ChrisJP-Embedded/midiSequencerInputUnit/Hardware/MidiSequencerInputUnit_6R_8C/Controller_Switch_Matrix_Module.kicad_sch

## KiCad design Hardware/MidiSequencerInputUnit_6R_8C/Controller_Switch_Matrix_Module.kicad_sch (2023-01-30)

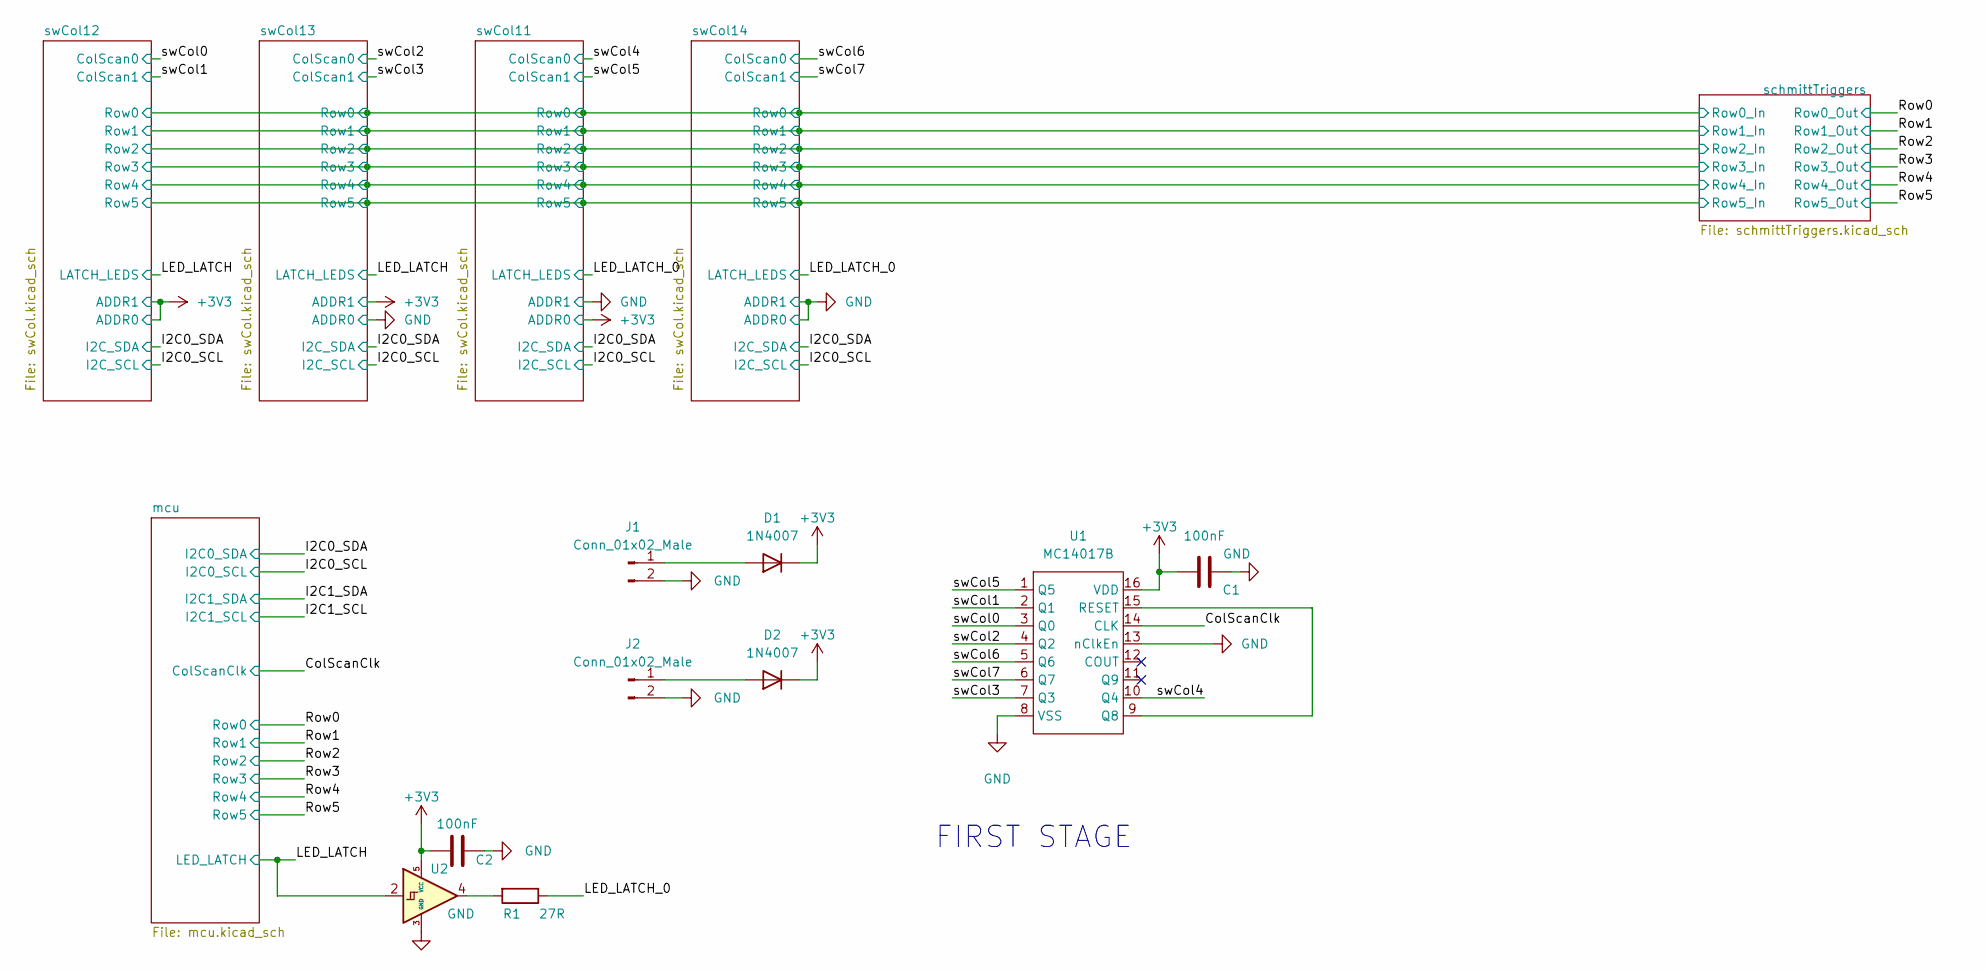
[picture p2: schematic Controller_Switch_Matrix_Module.kicad_sch]

Parts:
C1, C2: 100nF; C_0603_1608Metric; LCSC C14663
D1, D2: 1N4007; D_DO-41_SOD81_P10.16mm_Horizontal
J1, J2: Conn_01x02_Male; PinHeader_1x02_P2.54mm_Horizontal
R1: 27R; R_0603_1608Metric; LCSC C25190
U1: MC14017B; SOIC-16_3.9x9.9mm_P1.27mm; LCSC C512979
U2: SN74LVC1G17; SOT-23-5_HandSoldering; LCSC C7836

Connections:
+3V3: C1.1, C2.1, D1.1 (K), D2.1 (K), U1.16 (VDD), U2.5 (VCC)
ColScanClk: U1.14 (CLK)
GND: C1.2, C2.2, J1.2, J2.2, U1.8 (VSS), U1.13 (nClkEn), U2.3 (GND)
LED_LATCH: U2.2
LED_LATCH_0: R1.1
unnamed: D1.2 (A), J1.1
unnamed: D2.2 (A), J2.1
unnamed: R1.2, U2.4
unnamed: U1.9 (Q8), U1.15 (RESET)
swCol0: U1.3 (Q0)
swCol1: U1.2 (Q1)
swCol2: U1.4 (Q2)
swCol3: U1.7 (Q3)
swCol4: U1.10 (Q4)
swCol5: U1.1 (Q5)
swCol6: U1.5 (Q6)
swCol7: U1.6 (Q7)

Notes on the sheet:
FIRST STAGE
