ChrisJP-Embedded/midiSequencerInputUnit/Hardware/MidiSequencerInputUnit_6R_8C/Encoders.kicad_sch

## KiCad design Hardware/MidiSequencerInputUnit_6R_8C/Encoders.kicad_sch (2023-01-30)

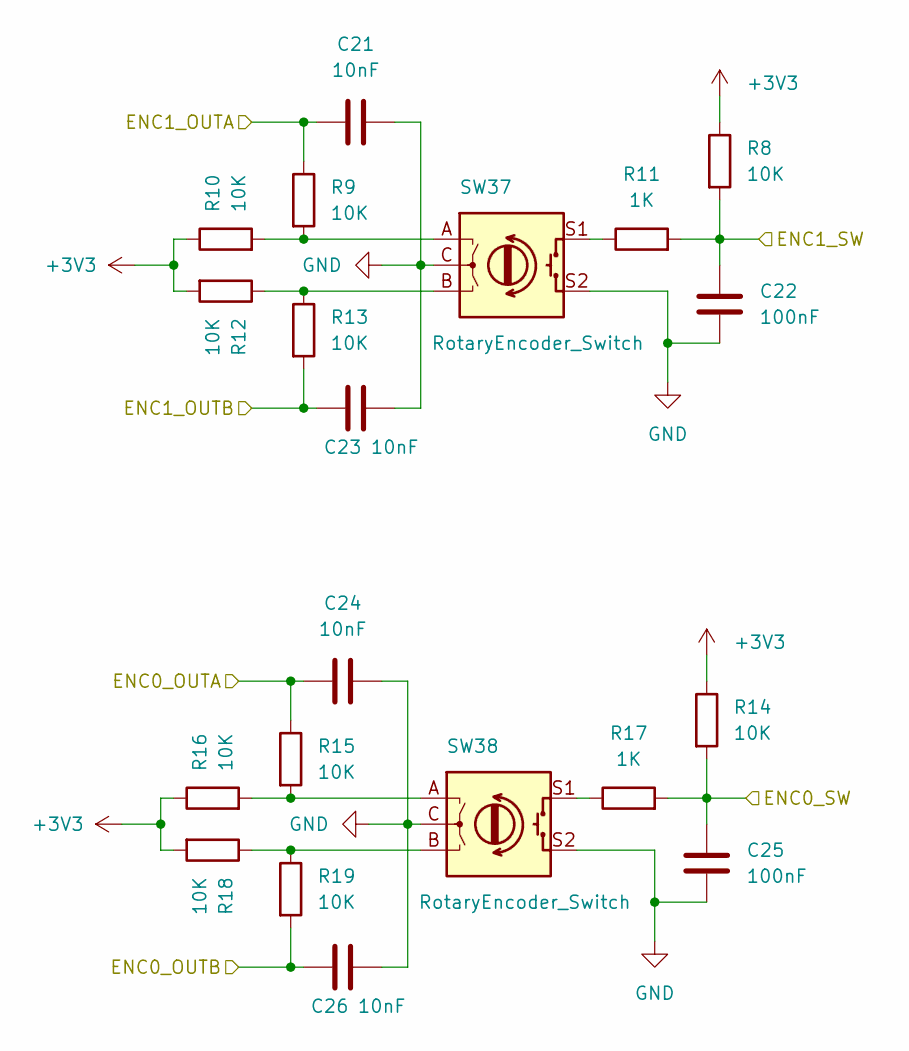
[picture p3: schematic Encoders.kicad_sch]

Parts:
C21, C23, C24, C26: 10nF; C_0603_1608Metric; LCSC C57112
C22, C25: 100nF; C_0603_1608Metric; LCSC C14663
R8, R9, R10, R12, R13, R14, R15, R16, R18, R19: 10K; R_0603_1608Metric; LCSC C25804
R11, R17: 1K; R_0603_1608Metric; LCSC C21190
SW37, SW38: RotaryEncoder_Switch; PEC11R-4220K-S0024

Connections:
+3V3: R8.1, R10.1, R12.2, R14.1, R16.1, R18.2
ENC0_OUTA: C24.1, R15.1
ENC0_OUTB: C26.1, R19.2
ENC0_SW: C25.1, R14.2, R17.2
ENC1_OUTA: C21.1, R9.1
ENC1_OUTB: C23.1, R13.2
ENC1_SW: C22.1, R8.2, R11.2
GND: C21.2, C22.2, C23.2, C24.2, C25.2, C26.2, SW37.C, SW37.S2, SW38.C, SW38.S2
unnamed: R9.2, R10.2, SW37.A
unnamed: R11.1, SW37.S1
unnamed: R12.1, R13.1, SW37.B
unnamed: R15.2, R16.2, SW38.A
unnamed: R17.1, SW38.S1
unnamed: R18.1, R19.1, SW38.B
