ChrisJP-Embedded/midiSequencerInputUnit/Hardware/MidiSequencerInputUnit_6R_8C/ips_screen.kicad_sch

## KiCad design Hardware/MidiSequencerInputUnit_6R_8C/ips_screen.kicad_sch (2023-01-30)

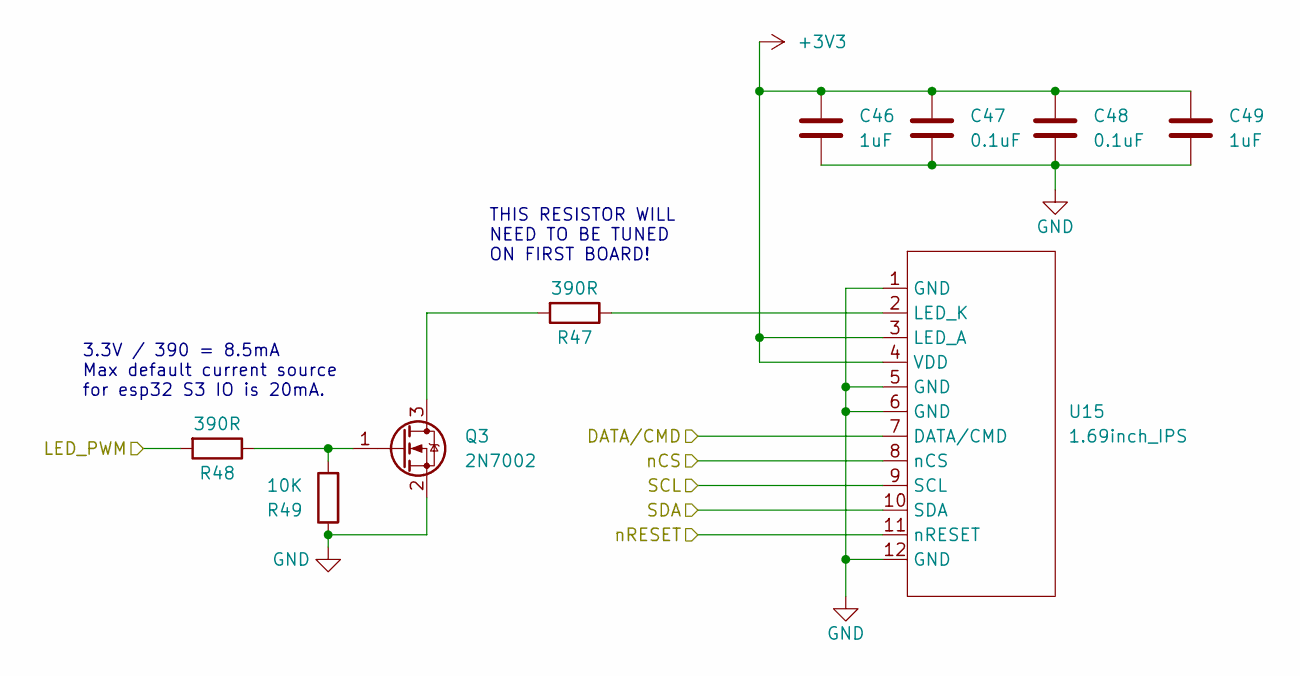
[picture p4: schematic ips_screen.kicad_sch]

Parts:
C46, C49: 1uF; C_0603_1608Metric; LCSC C15849
C47, C48: 0.1uF; C_0603_1608Metric; LCSC C14663
Q3: 2N7002; SOT-23; LCSC C8545
R47, R48: 390R; R_0603_1608Metric; LCSC C23151
R49: 10K; R_0603_1608Metric; LCSC C25804
U15: 1.69inch_IPS; 1.69inch IPS

Connections:
+3V3: C46.1, C47.1, C48.1, C49.1, U15.3 (LED_A), U15.4 (VDD)
DATA/CMD: U15.7 (DATA/CMD)
GND: C46.2, C47.2, C48.2, C49.2, Q3.2 (S), R49.1, U15.1 (GND), U15.5 (GND), U15.6 (GND), U15.12 (GND)
LED_PWM: R48.2
unnamed: Q3.1 (G), R48.1, R49.2
unnamed: Q3.3 (D), R47.2
unnamed: R47.1, U15.2 (LED_K)
SCL: U15.9 (SCL)
SDA: U15.10 (SDA)
nCS: U15.8 (nCS)
nRESET: U15.11 (nRESET)

Notes on the sheet:
3.3V / 390 = 8.5mA Max default current source for esp32 S3 IO is 20mA.
THIS RESISTOR WILL NEED TO BE TUNED ON FIRST BOARD!
