ChrisJP-Embedded/midiSequencerInputUnit/Hardware/MidiSequencerInputUnit_6R_8C/mcu.kicad_sch

## KiCad design Hardware/MidiSequencerInputUnit_6R_8C/mcu.kicad_sch (2023-01-30)

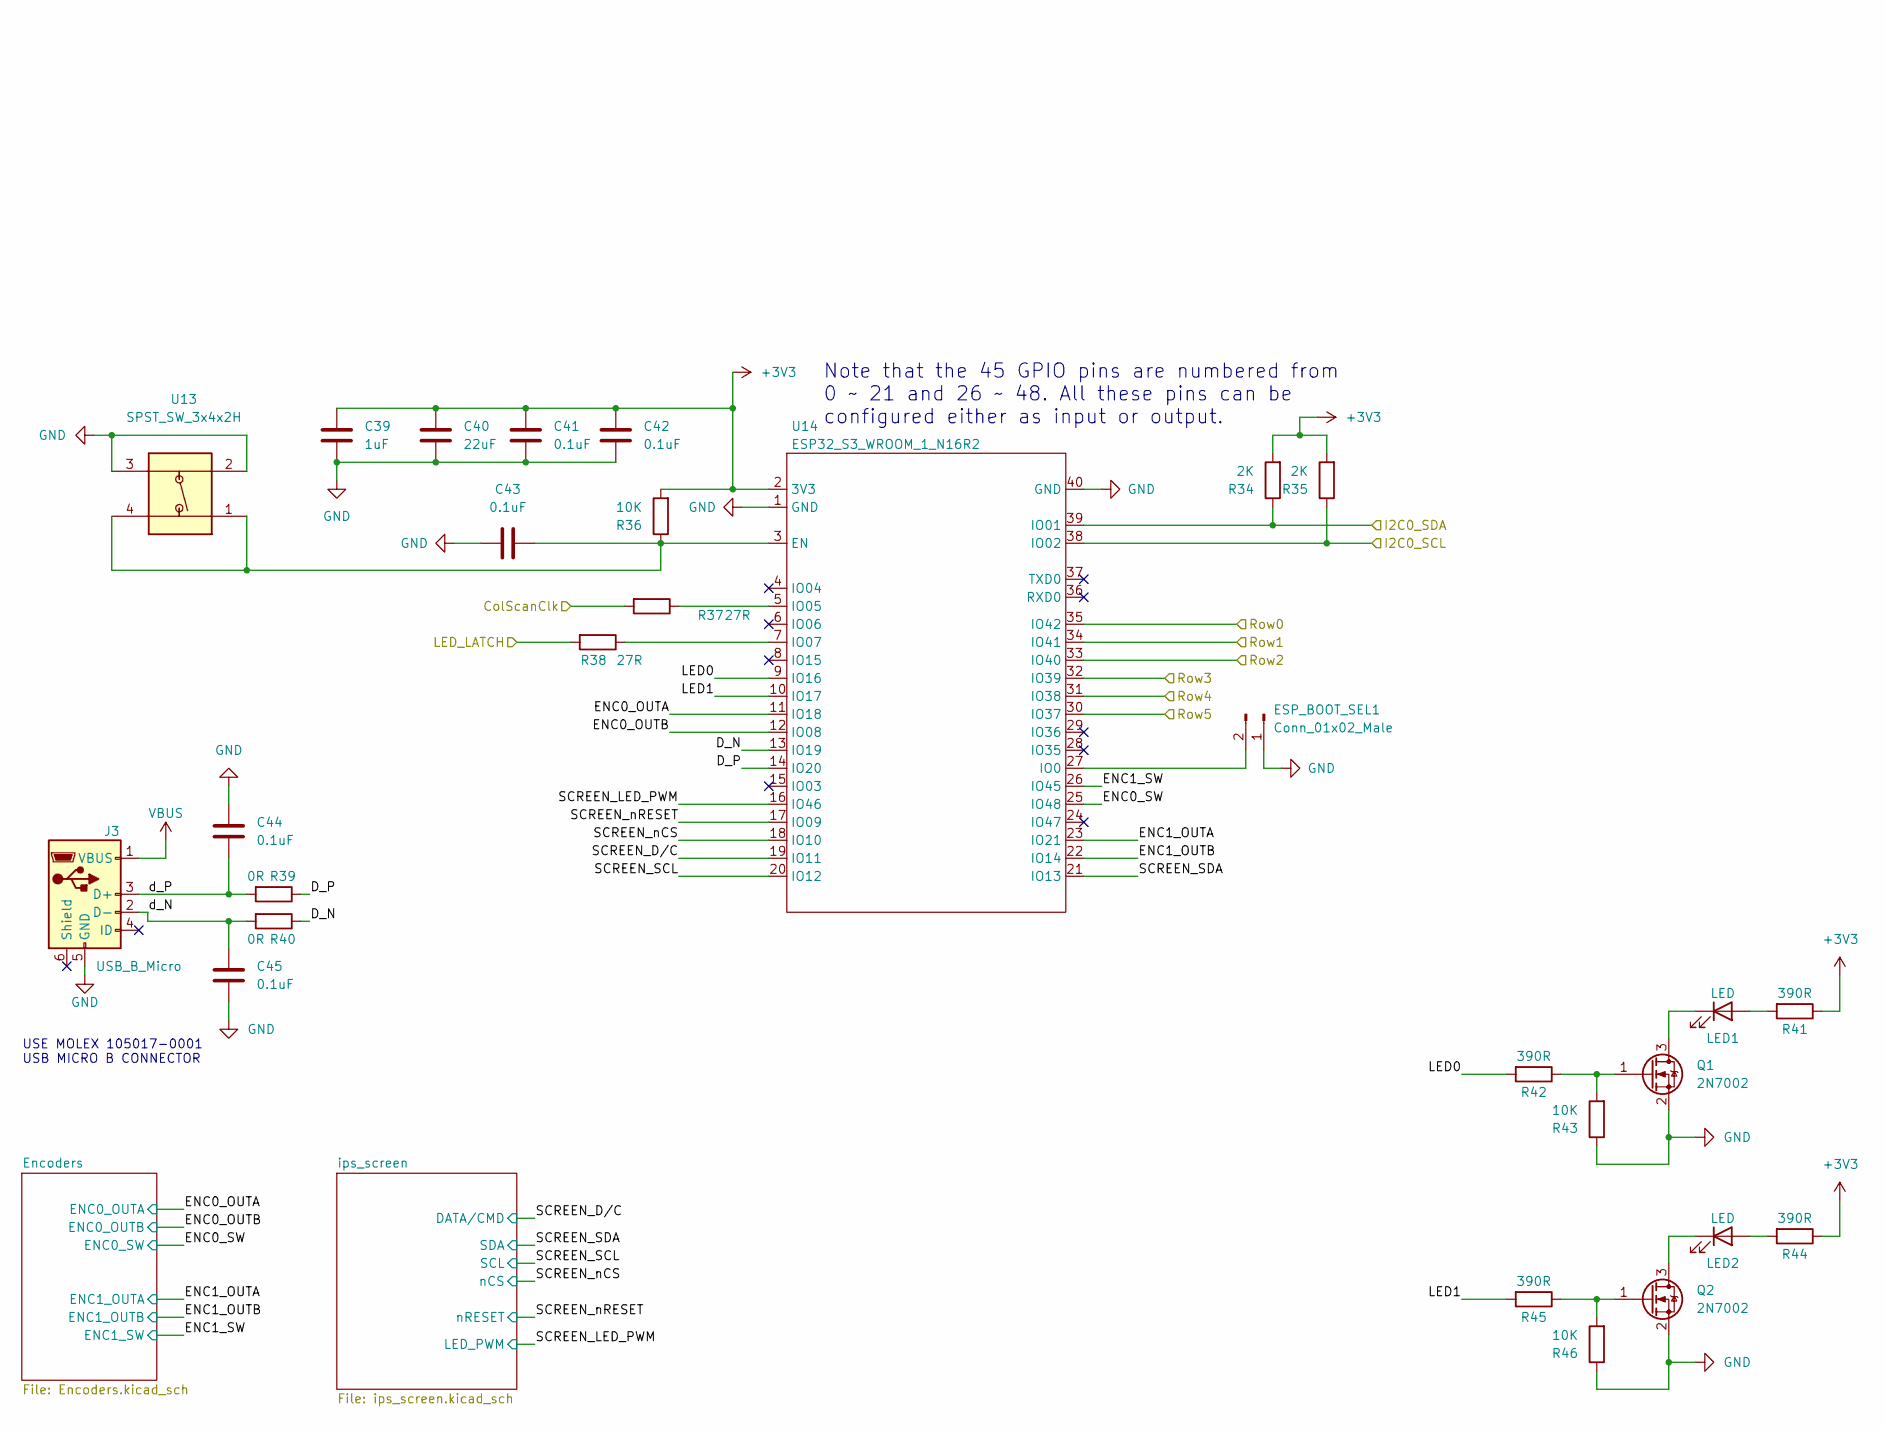
[picture p5: schematic mcu.kicad_sch]

Parts:
C39: 1uF; C_0603_1608Metric; LCSC C15849
C40: 22uF; C_0603_1608Metric; LCSC C59461
C41, C42, C43: 0.1uF; C_0603_1608Metric; LCSC C14663
C44, C45: 0.1uF; C_0603_1608Metric
ESP_BOOT_SEL1: Conn_01x02_Male; PinHeader_1x02_P2.54mm_Vertical
J3: USB_B_Micro; USB_Micro-B_Molex-105017-0001
LED1: LED; LED_0805_2012Metric; LCSC C84256
LED2: LED; LED_0805_2012Metric; LCSC C2296
Q1, Q2: 2N7002; SOT-23; LCSC C8545
R34, R35: 2K; R_0603_1608Metric; LCSC C22975
R36, R43, R46: 10K; R_0603_1608Metric; LCSC C25804
R37: 27R; R_0603_1608Metric
R38: 27R; R_0603_1608Metric; LCSC C25190
R39, R40: 0R; R_0603_1608Metric; LCSC C21189
R41, R42, R44, R45: 390R; R_0603_1608Metric; LCSC C23151
U13: SPST_SW_3x4x2H; SPST_SW_3x4X2
U14: ESP32_S3_WROOM_1_N16R2; ESP32-S3-WROOM-1

Connections:
+3V3: C39.1, C40.1, C41.1, C42.1, R34.2, R35.2, R36.2, R41.1, R44.1, U14.2 (3V3)
ColScanClk: R37.2
D_N: C45.1, J3.2 (D-), R40.1, R40.2, U14.13 (IO19)
D_P: C44.2, J3.3 (D+), R39.1, R39.2, U14.14 (IO20)
ENC0_OUTA: U14.11 (IO18)
ENC0_OUTB: U14.12 (IO08)
ENC0_SW: U14.25 (IO48)
ENC1_OUTA: U14.23 (IO21)
ENC1_OUTB: U14.22 (IO14)
ENC1_SW: U14.26 (IO45)
GND: C39.2, C40.2, C41.2, C42.2, C43.1, C44.1, C45.2, ESP_BOOT_SEL1.1, J3.5 (GND), Q1.2 (S), Q2.2 (S), R43.1, R46.1, U13.2, U13.3, U14.1 (GND), U14.40 (GND)
I2C0_SCL: R35.1, U14.38 (IO02)
I2C0_SDA: R34.1, U14.39 (IO01)
LED0: R42.2, U14.9 (IO16)
LED1: R45.2, U14.10 (IO17)
LED_LATCH: R38.2
unnamed: C43.2, R36.1, U13.1, U13.4, U14.3 (EN)
unnamed: ESP_BOOT_SEL1.2, U14.27 (IO0)
unnamed: LED1.1 (K), Q1.3 (D)
unnamed: LED1.2 (A), R41.2
unnamed: LED2.1 (K), Q2.3 (D)
unnamed: LED2.2 (A), R44.2
unnamed: Q1.1 (G), R42.1, R43.2
unnamed: Q2.1 (G), R45.1, R46.2
unnamed: R37.1, U14.5 (IO05)
unnamed: R38.1, U14.7 (IO07)
Row0: U14.35 (IO42)
Row1: U14.34 (IO41)
Row2: U14.33 (IO40)
Row3: U14.32 (IO39)
Row4: U14.31 (IO38)
Row5: U14.30 (IO37)
SCREEN_D/C: U14.19 (IO11)
SCREEN_LED_PWM: U14.16 (IO46)
SCREEN_SCL: U14.20 (IO12)
SCREEN_SDA: U14.21 (IO13)
SCREEN_nCS: U14.18 (IO10)
SCREEN_nRESET: U14.17 (IO09)
VBUS: J3.1 (VBUS)

Notes on the sheet:
USE MOLEX 105017-0001 USB MICRO B CONNECTOR
Note that the 45 GPIO pins are numbered from 0 ~ 21 and 26 ~ 48. All these pins can be configured either as input or output.
