ChrisJP-Embedded/midiSequencerInputUnit/Hardware/MidiSequencerInputUnit_6R_8C/schmittTriggers.kicad_sch

## KiCad design Hardware/MidiSequencerInputUnit_6R_8C/schmittTriggers.kicad_sch (2023-01-30)

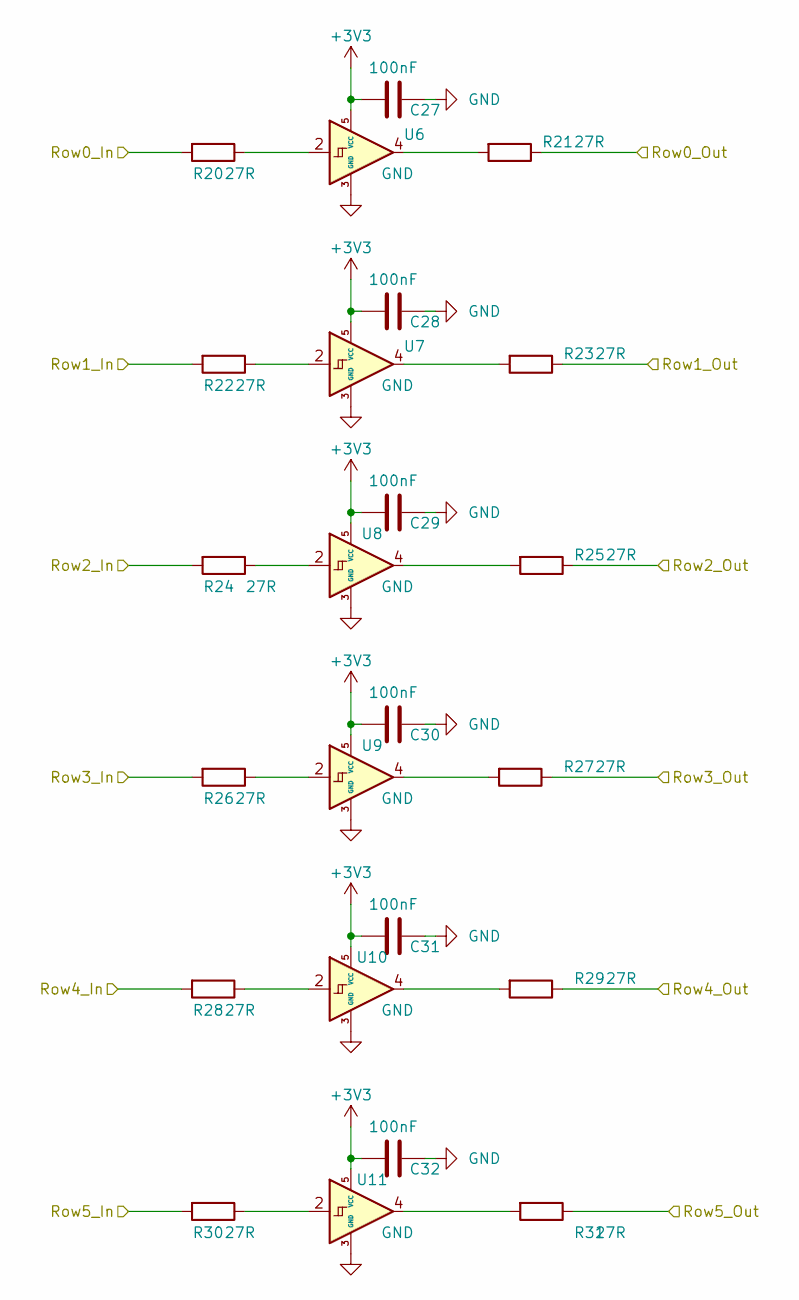
[picture p6: schematic schmittTriggers.kicad_sch]

Parts:
C27, C28, C29, C30, C31, C32: 100nF; C_0603_1608Metric; LCSC C14663
R20, R21, R22, R23, R24, R25, R26, R27, R28, R29, R30, R31: 27R; R_0603_1608Metric; LCSC C25190
U6, U7, U8, U9, U10, U11: SN74LVC1G17; SOT-23-5_HandSoldering; LCSC C7836

Connections:
+3V3: C27.1, C28.1, C29.1, C30.1, C31.1, C32.1, U6.5 (VCC), U7.5 (VCC), U8.5 (VCC), U9.5 (VCC), U10.5 (VCC), U11.5 (VCC)
GND: C27.2, C28.2, C29.2, C30.2, C31.2, C32.2, U6.3 (GND), U7.3 (GND), U8.3 (GND), U9.3 (GND), U10.3 (GND), U11.3 (GND)
unnamed: R20.1, U6.2
unnamed: R21.2, U6.4
unnamed: R22.1, U7.2
unnamed: R23.2, U7.4
unnamed: R24.1, U8.2
unnamed: R25.2, U8.4
unnamed: R26.1, U9.2
unnamed: R27.2, U9.4
unnamed: R28.1, U10.2
unnamed: R29.2, U10.4
unnamed: R30.1, U11.2
unnamed: R31.2, U11.4
Row0_In: R20.2
Row0_Out: R21.1
Row1_In: R22.2
Row1_Out: R23.1
Row2_In: R24.2
Row2_Out: R25.1
Row3_In: R26.2
Row3_Out: R27.1
Row4_In: R28.2
Row4_Out: R29.1
Row5_In: R30.2
Row5_Out: R31.1
