ChrisJP-Embedded/midiSequencerInputUnit/Hardware/MidiSequencerInputUnit_6R_8C/swCol.kicad_sch

## KiCad design Hardware/MidiSequencerInputUnit_6R_8C/swCol.kicad_sch (2023-01-30)

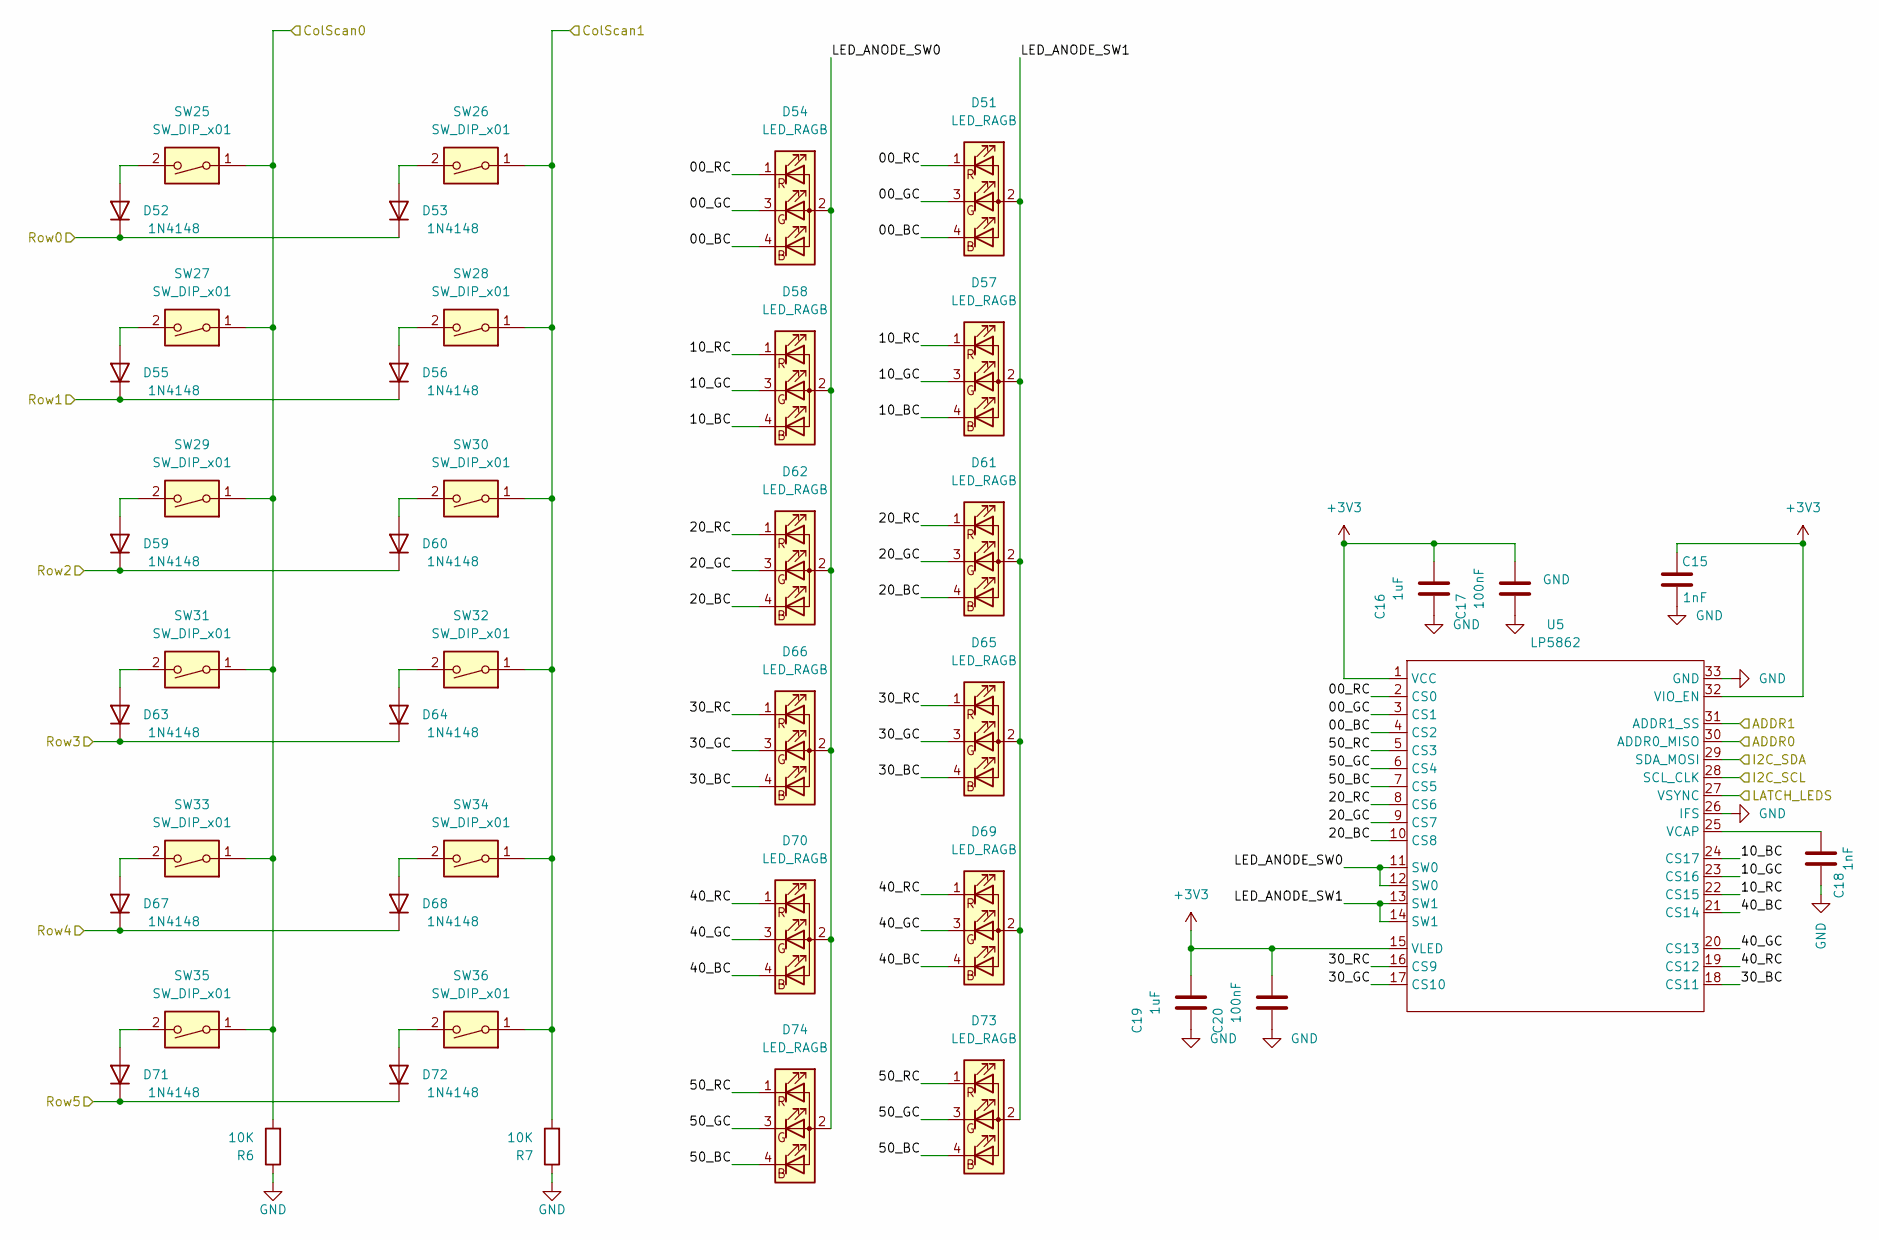
[picture p7: schematic swCol.kicad_sch]

Parts:
C15, C18: 1nF; C_0603_1608Metric; LCSC C1588
C16, C19: 1uF; C_0603_1608Metric; LCSC C15849
C17, C20: 100nF; C_0603_1608Metric; LCSC C14663
D51, D54, D57, D58, D61, D62, D65, D66, D69, D70, D73, D74: LED_RAGB; RGB_LED_1206; LCSC C375571
D52, D53, D55, D56, D59, D60, D63, D64, D67, D68, D71, D72: 1N4148; D_SOD-323; LCSC C2128
R6, R7: 10K; R_0603_1608Metric; LCSC C25804
SW25, SW26, SW27, SW28, SW29, SW30, SW31, SW32, SW33, SW34, SW35, SW36: SW_DIP_x01; GATERON_KS-27_KBSW
U5: LP5862; VQFN-32_LP5864

Connections:
00_BC: D51.4 (BK), D54.4 (BK), U5.4 (CS2)
00_GC: D51.3 (GK), D54.3 (GK), U5.3 (CS1)
00_RC: D51.1 (RK), D54.1 (RK), U5.2 (CS0)
10_BC: D57.4 (BK), D58.4 (BK), U5.24 (CS17)
10_GC: D57.3 (GK), D58.3 (GK), U5.23 (CS16)
10_RC: D57.1 (RK), D58.1 (RK), U5.22 (CS15)
20_BC: D61.4 (BK), D62.4 (BK), U5.10 (CS8)
20_GC: D61.3 (GK), D62.3 (GK), U5.9 (CS7)
20_RC: D61.1 (RK), D62.1 (RK), U5.8 (CS6)
30_BC: D65.4 (BK), D66.4 (BK), U5.18 (CS11)
30_GC: D65.3 (GK), D66.3 (GK), U5.17 (CS10)
30_RC: D65.1 (RK), D66.1 (RK), U5.16 (CS9)
40_BC: D69.4 (BK), D70.4 (BK), U5.21 (CS14)
40_GC: D69.3 (GK), D70.3 (GK), U5.20 (CS13)
40_RC: D69.1 (RK), D70.1 (RK), U5.19 (CS12)
50_BC: D73.4 (BK), D74.4 (BK), U5.7 (CS5)
50_GC: D73.3 (GK), D74.3 (GK), U5.6 (CS4)
50_RC: D73.1 (RK), D74.1 (RK), U5.5 (CS3)
+3V3: C15.1, C16.2, C17.2, C19.2, C20.2, U5.1 (VCC), U5.15 (VLED), U5.32 (VIO_EN)
ADDR0: U5.30 (ADDR0_MISO)
ADDR1: U5.31 (ADDR1_SS)
ColScan0: R6.2, SW25.1, SW27.1, SW29.1, SW31.1, SW33.1, SW35.1
ColScan1: R7.2, SW26.1, SW28.1, SW30.1, SW32.1, SW34.1, SW36.1
GND: C15.2, C16.1, C17.1, C18.1, C19.1, C20.1, R6.1, R7.1, U5.26 (IFS), U5.33 (GND)
I2C_SCL: U5.28 (SCL_CLK)
I2C_SDA: U5.29 (SDA_MOSI)
LATCH_LEDS: U5.27 (VSYNC)
LED_ANODE_SW0: D54.2 (A), D58.2 (A), D62.2 (A), D66.2 (A), D70.2 (A), D74.2 (A), U5.11 (SW0), U5.12 (SW0)
LED_ANODE_SW1: D51.2 (A), D57.2 (A), D61.2 (A), D65.2 (A), D69.2 (A), D73.2 (A), U5.13 (SW1), U5.14 (SW1)
unnamed: C18.2, U5.25 (VCAP)
unnamed: D52.2 (A), SW25.2
unnamed: D53.2 (A), SW26.2
unnamed: D55.2 (A), SW27.2
unnamed: D56.2 (A), SW28.2
unnamed: D59.2 (A), SW29.2
unnamed: D60.2 (A), SW30.2
unnamed: D63.2 (A), SW31.2
unnamed: D64.2 (A), SW32.2
unnamed: D67.2 (A), SW33.2
unnamed: D68.2 (A), SW34.2
unnamed: D71.2 (A), SW35.2
unnamed: D72.2 (A), SW36.2
Row0: D52.1 (K), D53.1 (K)
Row1: D55.1 (K), D56.1 (K)
Row2: D59.1 (K), D60.1 (K)
Row3: D63.1 (K), D64.1 (K)
Row4: D67.1 (K), D68.1 (K)
Row5: D71.1 (K), D72.1 (K)
