ChrisJP-Embedded/midiSequencerInputUnit/Hardware/MidiSequencerInputUnit_6R_8C/swLastCol.kicad_sch

## KiCad design Hardware/MidiSequencerInputUnit_6R_8C/swLastCol.kicad_sch (2023-01-30)

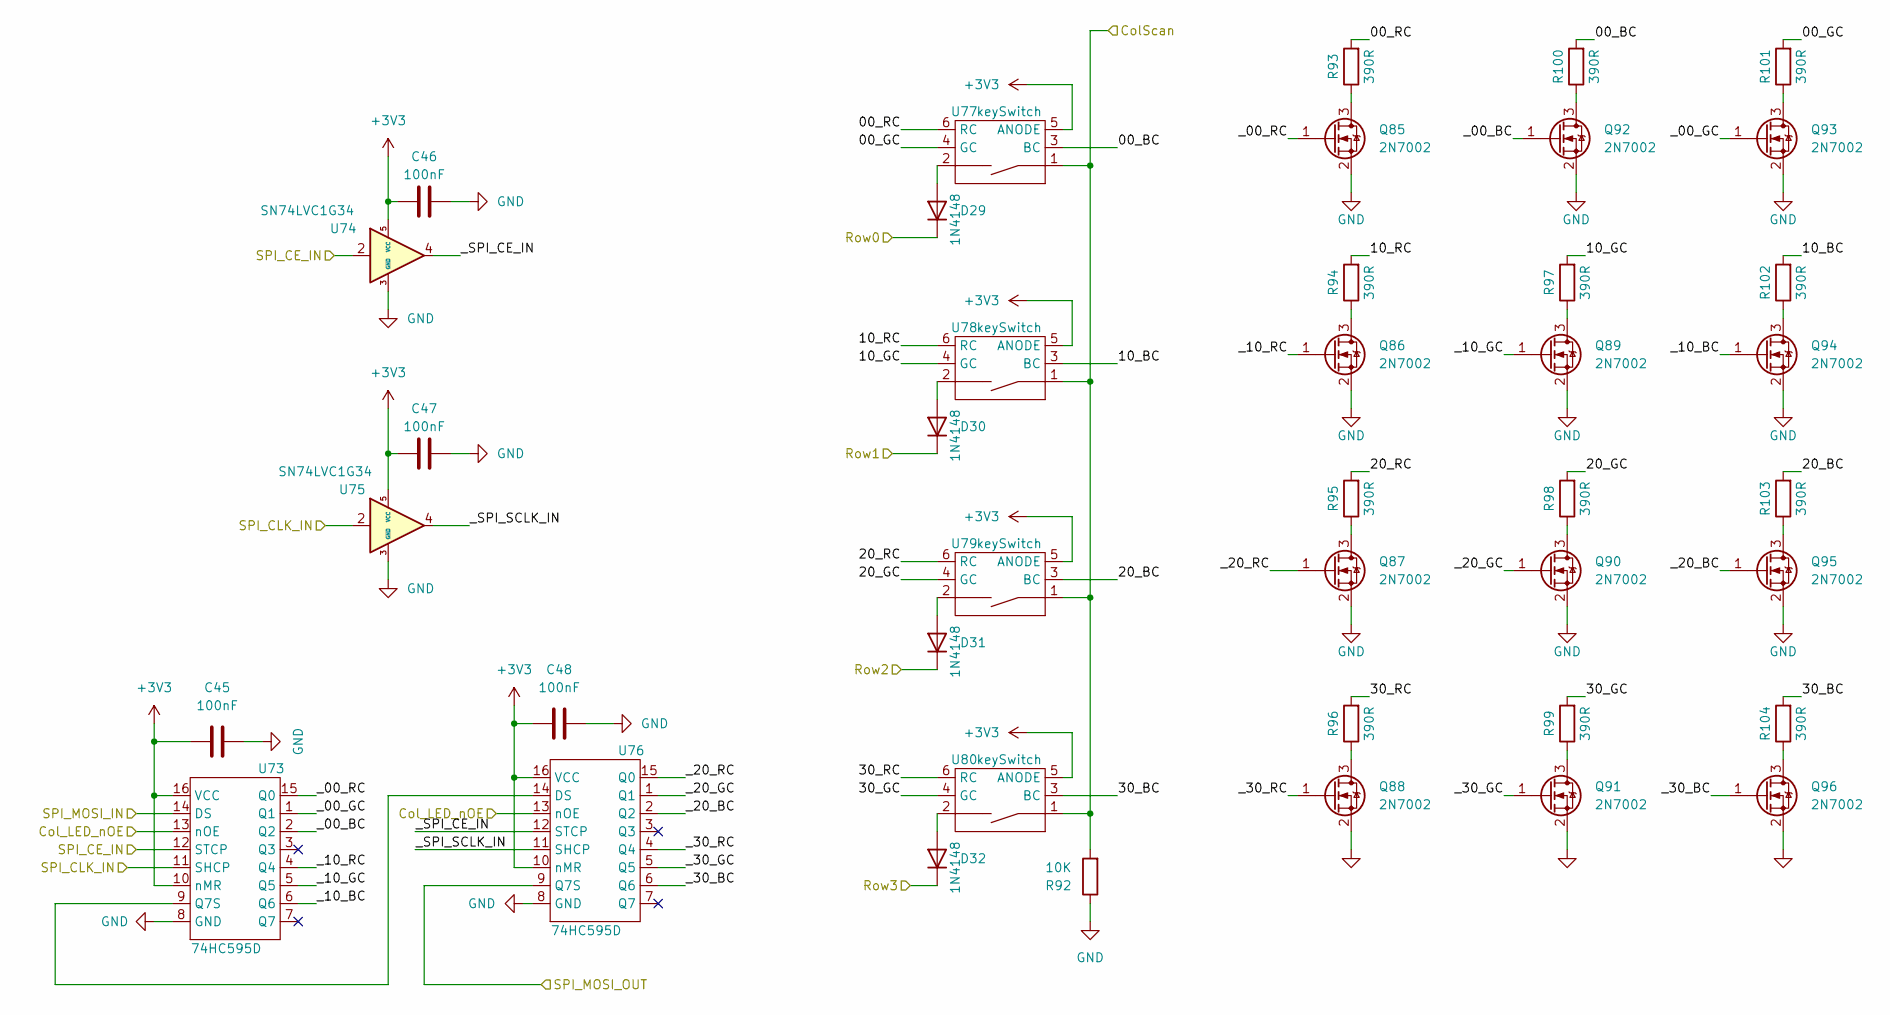
[picture p8: schematic swLastCol.kicad_sch]

Parts:
C45, C46, C47, C48: 100nF; C_0603_1608Metric; LCSC C14663
D29, D30, D31, D32: 1N4148; D_0603_1608Metric
Q85, Q86, Q87, Q88, Q89, Q90, Q91, Q92, Q93, Q94, Q95, Q96: 2N7002; SOT-23
R92: 10K; R_0603_1608Metric; LCSC C25804
R93, R94, R95, R96, R97, R98, R99, R100, R101, R102, R103, R104: 390R; R_0603_1608Metric; LCSC C23151
U73, U76: 74HC595D; SOIC-16_3.9x9.9mm_P1.27mm; LCSC C5947
U74, U75: SN74LVC1G34; SOT-23-5; LCSC C840096
U77, U78, U79, U80: keySwitch; KEYBOARD_SWITCH

Connections:
00_BC: R100.2, U77.3 (BC)
00_GC: R101.2, U77.4 (GC)
00_RC: R93.2, U77.6 (RC)
10_BC: R102.2, U78.3 (BC)
10_GC: R97.2, U78.4 (GC)
10_RC: R94.2, U78.6 (RC)
20_BC: R103.2, U79.3 (BC)
20_GC: R98.2, U79.4 (GC)
20_RC: R95.2, U79.6 (RC)
30_BC: R104.2, U80.3 (BC)
30_GC: R99.2, U80.4 (GC)
30_RC: R96.2, U80.6 (RC)
+3V3: C45.1, C46.1, C47.1, C48.1, U73.10 (nMR), U73.16 (VCC), U74.5 (VCC), U75.5 (VCC), U76.10 (nMR), U76.16 (VCC), U77.5 (ANODE), U78.5 (ANODE), U79.5 (ANODE), U80.5 (ANODE)
ColScan: R92.2, U77.1, U78.1, U79.1, U80.1
Col_LED_nOE: U73.13 (nOE), U76.13 (nOE)
GND: C45.2, C46.2, C47.2, C48.2, Q85.2 (S), Q86.2 (S), Q87.2 (S), Q89.2 (S), Q90.2 (S), Q92.2 (S), Q93.2 (S), Q94.2 (S), Q95.2 (S), R92.1, U73.8 (GND), U74.3 (GND), U75.3 (GND), U76.8 (GND)
unnamed: D29.2 (A), U77.2
unnamed: D30.2 (A), U78.2
unnamed: D31.2 (A), U79.2
unnamed: D32.2 (A), U80.2
unnamed: Q85.3 (D), R93.1
unnamed: Q86.3 (D), R94.1
unnamed: Q87.3 (D), R95.1
unnamed: Q88.3 (D), R96.1
unnamed: Q89.3 (D), R97.1
unnamed: Q90.3 (D), R98.1
unnamed: Q91.3 (D), R99.1
unnamed: Q92.3 (D), R100.1
unnamed: Q93.3 (D), R101.1
unnamed: Q94.3 (D), R102.1
unnamed: Q95.3 (D), R103.1
unnamed: Q96.3 (D), R104.1
unnamed: U73.9 (Q7S), U76.14 (DS)
Row0: D29.1 (K)
Row1: D30.1 (K)
Row2: D31.1 (K)
Row3: D32.1 (K)
SPI_CE_IN: U73.12 (STCP), U74.2
SPI_CLK_IN: U73.11 (SHCP), U75.2
SPI_MOSI_IN: U73.14 (DS)
SPI_MOSI_OUT: U76.9 (Q7S)
_00_BC: Q92.1 (G), U73.2 (Q2)
_00_GC: Q93.1 (G), U73.1 (Q1)
_00_RC: Q85.1 (G), U73.15 (Q0)
_10_BC: Q94.1 (G), U73.6 (Q6)
_10_GC: Q89.1 (G), U73.5 (Q5)
_10_RC: Q86.1 (G), U73.4 (Q4)
_20_BC: Q95.1 (G), U76.2 (Q2)
_20_GC: Q90.1 (G), U76.1 (Q1)
_20_RC: Q87.1 (G), U76.15 (Q0)
_30_BC: Q96.1 (G), U76.6 (Q6)
_30_GC: Q91.1 (G), U76.5 (Q5)
_30_RC: Q88.1 (G), U76.4 (Q4)
_SPI_CE_IN: U74.4, U76.12 (STCP)
_SPI_SCLK_IN: U75.4, U76.11 (SHCP)
~: Q88.2 (S), Q91.2 (S), Q96.2 (S)
